makerspacelt/NTAduino/kicad_project/ntaduino.sch

## KiCad design kicad_project/ntaduino.sch (2014-07-19)

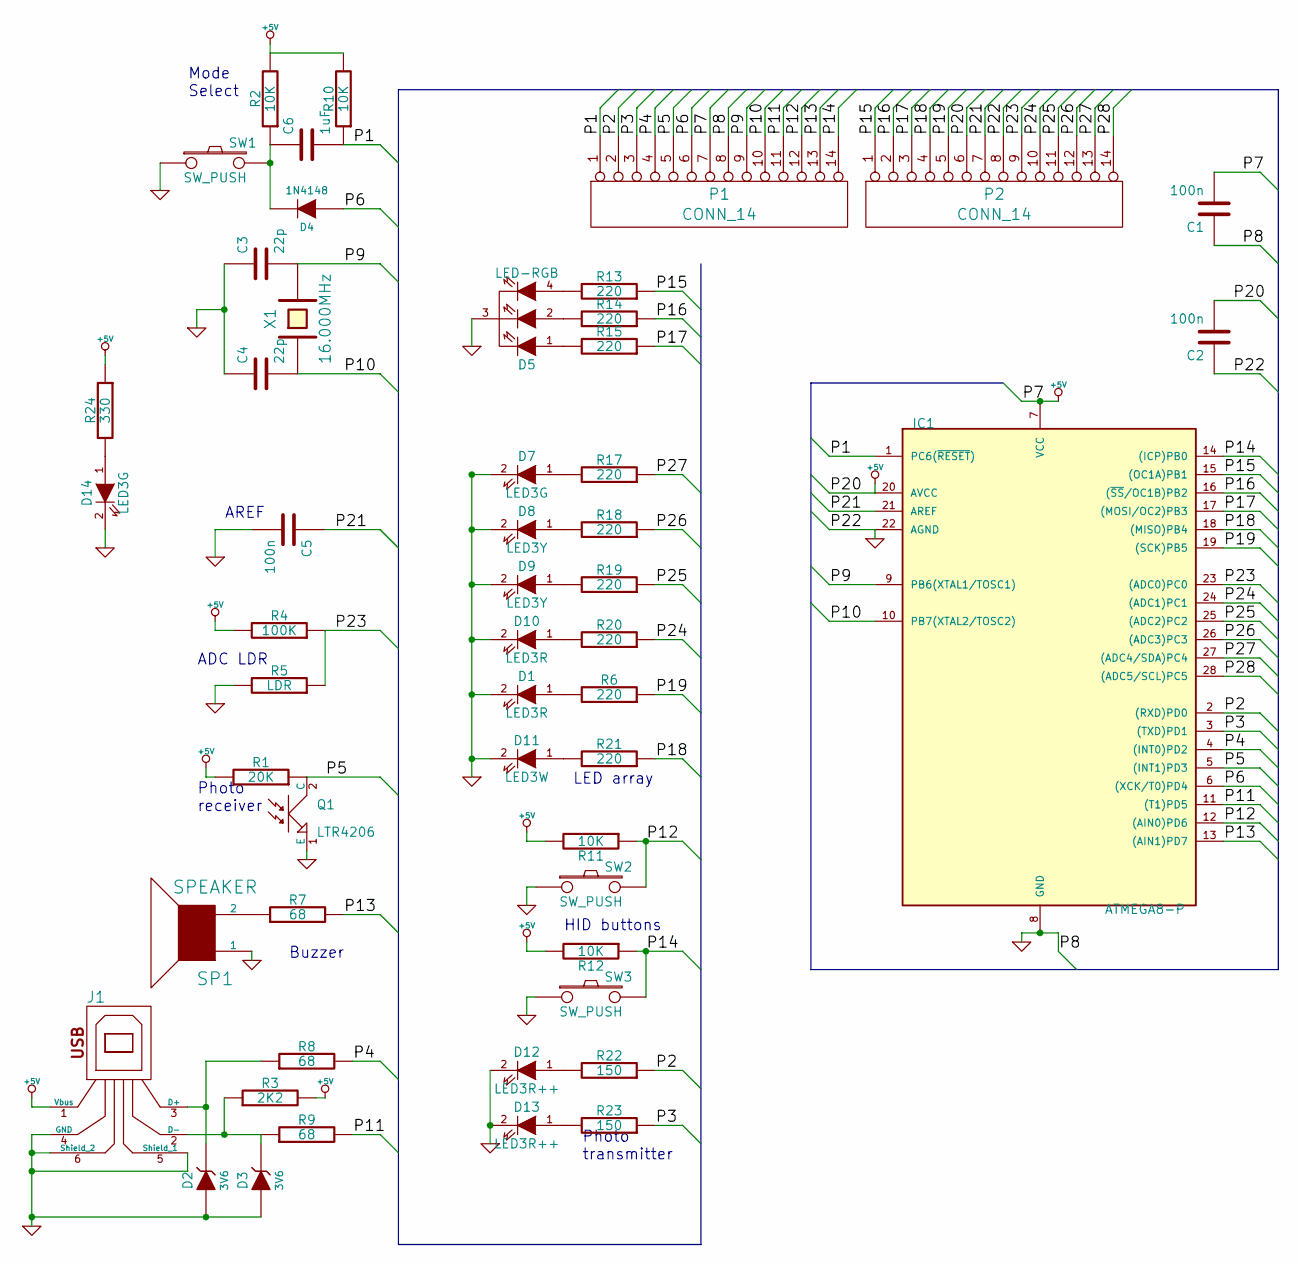
[picture p3: schematic ntaduino.sch]

Parts:
C1, C2, C5: 100n
C3, C4: 22p
C6: 1uF
D1, D10: LED3R
D2, D3: 3V6
D4: 1N4148
D5: LED-RGB
D7, D14: LED3G
D8, D9: LED3Y
D11: LED3W
D12, D13: LED3R++
IC1: ATMEGA8-P; DIL28
J1: USB_1
P1, P2: CONN_14
Q1: LTR4206
R1: 20K
R2, R10, R11, R12: 10K
R3: 2K2
R4: 100K
R5: LDR
R6, R13, R14, R15, R17, R18, R19, R20, R21: 220
R7, R8, R9: 68
R22, R23: 150
R24: 330
SP1: SPEAKER
SW1, SW2, SW3: SW_PUSH
X1: 16.000MHz

Connections:
+5V: C1.2, C2.2, IC1.7 (VCC), IC1.20 (AVCC), J1.1 (Vbus), P1.7, P2.6, R1.2, R2.2, R3.2, R4.2, R10.2, R11.2, R12.2, R24.1
GND: C1.1, C2.1, C3.1, C4.1, C5.2, D1.2 (K), D2.1 (A), D3.1 (A), D5.3 (C), D7.2 (K), D8.2 (K), D9.2 (K), D10.2 (K), D11.2 (K), D12.2 (K), D13.2 (K), D14.2 (K), IC1.8 (GND), IC1.22 (AGND), J1.4 (GND), J1.5 (Shield_1), J1.6 (Shield_2), P1.8, P2.8, Q1.1 (E), R5.2, SP1.1, SW1.1, SW2.1, SW3.1
unnamed: C6.1, D4.2 (K), R2.1, SW1.2
unnamed: D1.1 (A), R6.2
unnamed: D2.2 (K), J1.3 (D+), R8.1
unnamed: D3.2 (K), J1.2 (D-), R3.1, R9.1
unnamed: D5.1 (G), R15.2
unnamed: D5.2 (B), R14.2
unnamed: D5.4 (R), R13.2
unnamed: D7.1 (A), R17.2
unnamed: D8.1 (A), R18.2
unnamed: D9.1 (A), R19.2
unnamed: D10.1 (A), R20.2
unnamed: D11.1 (A), R21.2
unnamed: D12.1 (A), R22.2
unnamed: D13.1 (A), R23.2
unnamed: D14.1 (A), R24.2
unnamed: R7.1, SP1.2
P1: C6.2, IC1.1 (PC6(~RESET~)), P1.1, R10.1
P2: IC1.2 ((RXD)PD0), P1.2, R22.1
P3: IC1.3 ((TXD)PD1), P1.3, R23.1
P4: IC1.4 ((INT0)PD2), P1.4, R8.2
P5: IC1.5 ((INT1)PD3), P1.5, Q1.2 (C), R1.1
P6: D4.1 (A), IC1.6 ((XCK/T0)PD4), P1.6
P9: C3.2, IC1.9 (PB6(XTAL1/TOSC1)), P1.9, X1.2
P10: C4.2, IC1.10 (PB7(XTAL2/TOSC2)), P1.10, X1.1
P11: IC1.11 ((T1)PD5), P1.11, R9.2
P12: IC1.12 ((AIN0)PD6), P1.12, R11.1, SW2.2
P13: IC1.13 ((AIN1)PD7), P1.13, R7.2
P14: IC1.14 ((ICP)PB0), P1.14, R12.1, SW3.2
P15: IC1.15 ((OC1A)PB1), P2.1, R13.1
P16: IC1.16 ((~SS~/OC1B)PB2), P2.2, R14.1
P17: IC1.17 ((MOSI/OC2)PB3), P2.3, R15.1
P18: IC1.18 ((MISO)PB4), P2.4, R21.1
P19: IC1.19 ((SCK)PB5), P2.5, R6.1
P21: C5.1, IC1.21 (AREF), P2.7
P23: IC1.23 ((ADC0)PC0), P2.9, R4.1, R5.1
P24: IC1.24 ((ADC1)PC1), P2.10, R20.1
P25: IC1.25 ((ADC2)PC2), P2.11, R19.1
P26: IC1.26 ((ADC3)PC3), P2.12, R18.1
P27: IC1.27 ((ADC4/SDA)PC4), P2.13, R17.1
P28: IC1.28 ((ADC5/SCL)PC5), P2.14

Notes on the sheet:
LED array
HID buttons
Photo transmitter
Buzzer
Photo receiver
ADC LDR
Mode Select
AREF
